Runningtarrens/Msweep/pics/PXL_20230211_223605693.jpg

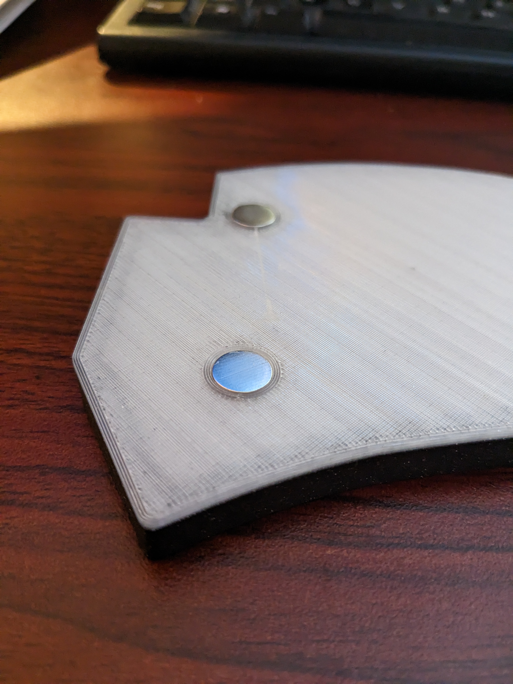
pics/PXL_20230211_223605693.jpg
