Runningtarrens/Msweep/pics/PXL_20230214_120325420.jpg

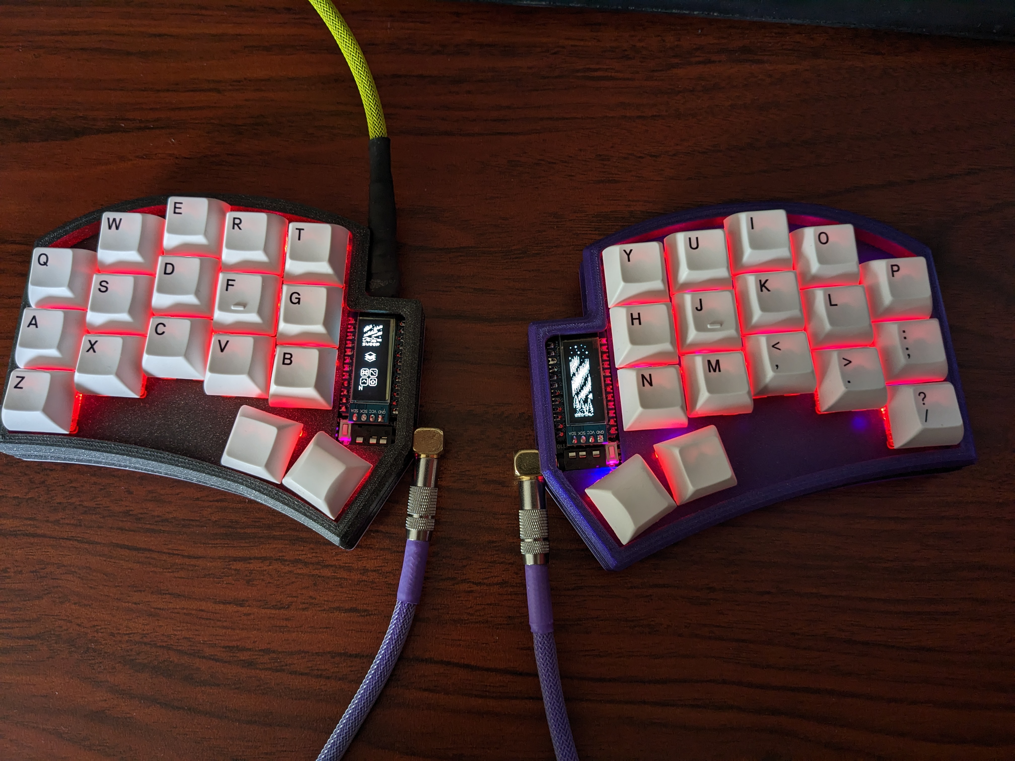
pics/PXL_20230214_120325420.jpg
