Runningtarrens/Msweep/pics/PXL_20230214_122314596.jpg

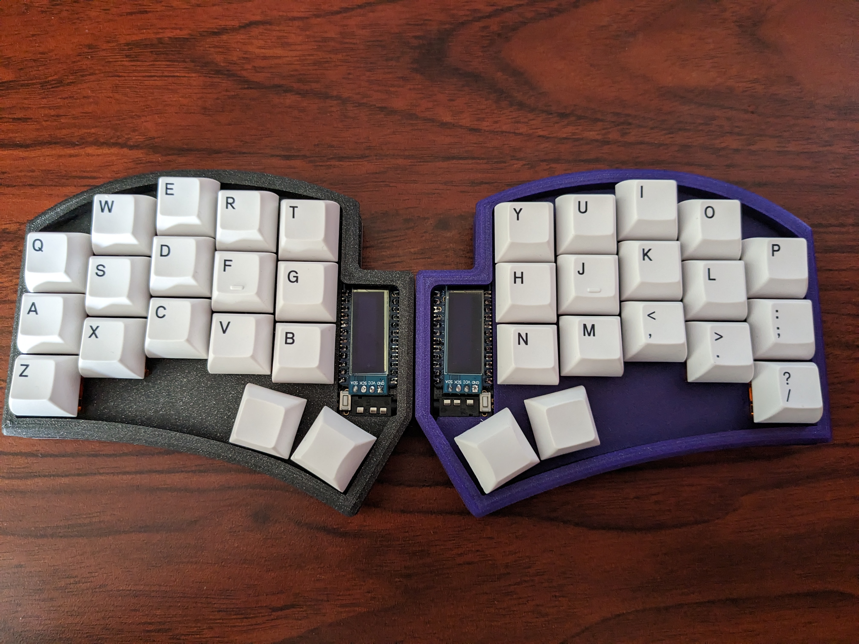
pics/PXL_20230214_122314596.jpg
