Runningtarrens/Msweep/pics/PXL_20230214_122454524.jpg

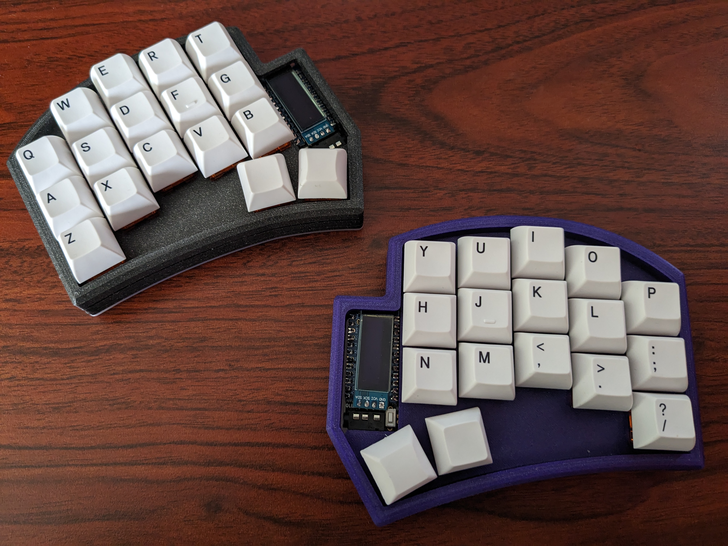
pics/PXL_20230214_122454524.jpg
