Runningtarrens/Msweep/pics/PXL_20230216_065255677.jpg

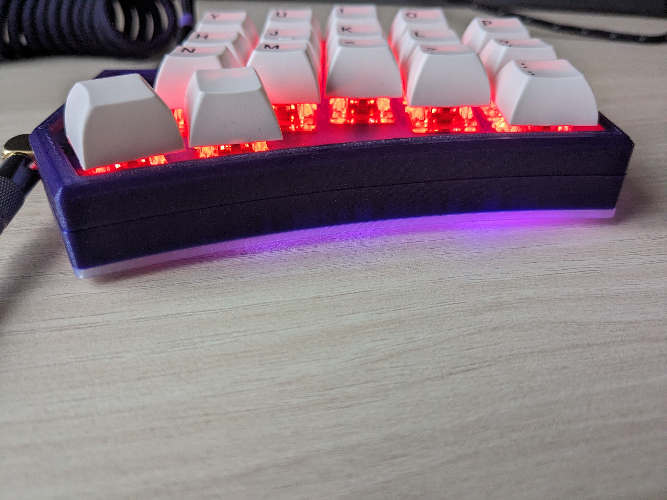
pics/PXL_20230216_065255677.jpg
