Runningtarrens/Msweep/pics/PXL_20230216_065311987.jpg

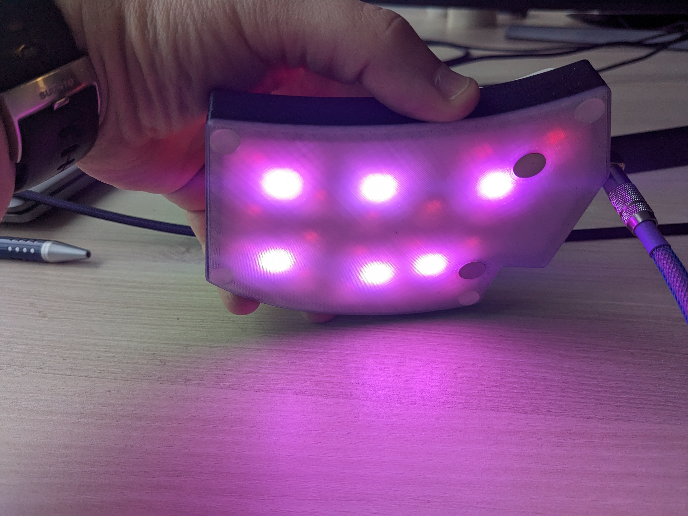
pics/PXL_20230216_065311987.jpg
