Runningtarrens/Msweep/pics/PXL_20230216_065402913.jpg

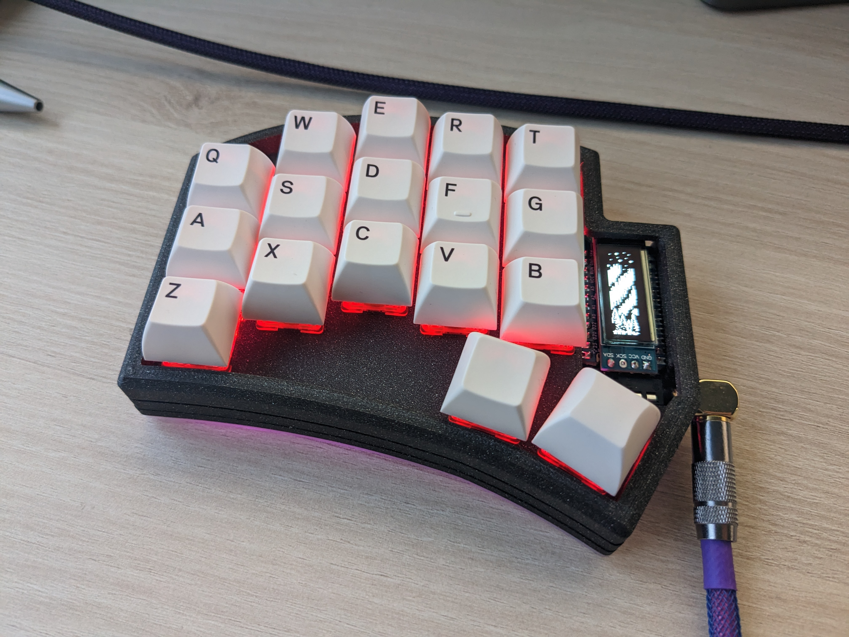
pics/PXL_20230216_065402913.jpg
