Runningtarrens/Msweep/pics/PXL_20230216_065406352.jpg

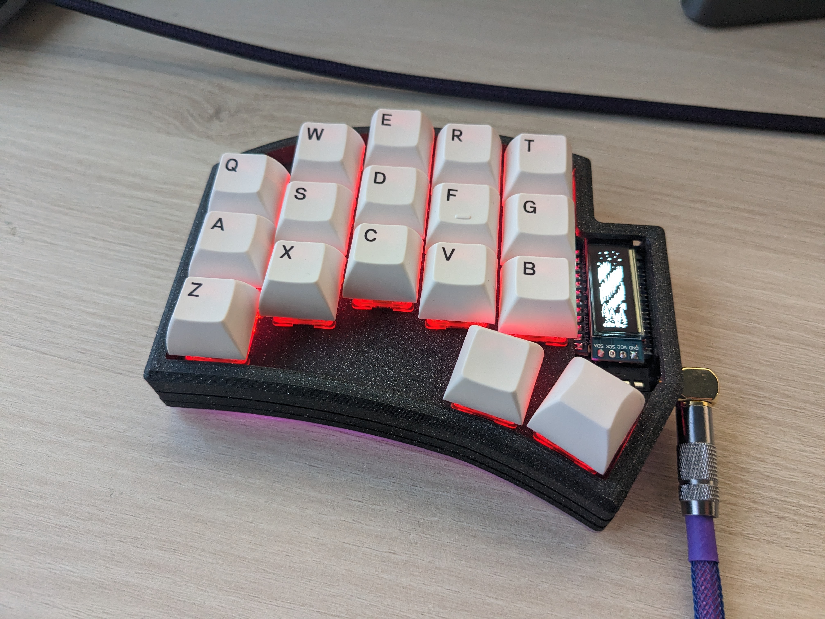
pics/PXL_20230216_065406352.jpg
