Runningtarrens/Msweep/pics/PXL_20230216_125020288.jpg

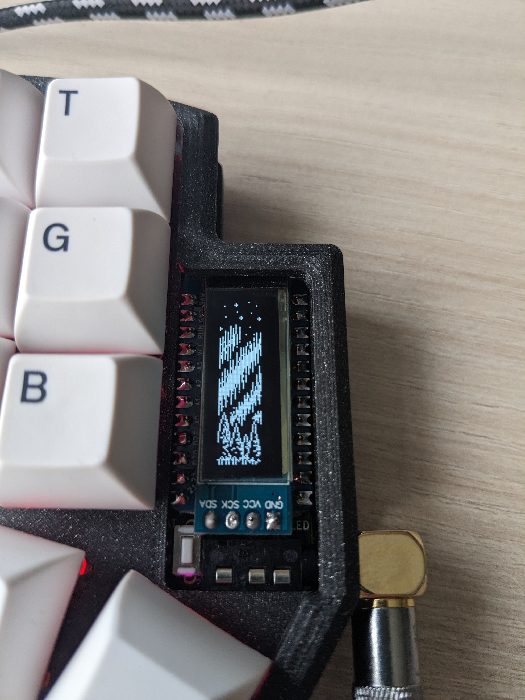
pics/PXL_20230216_125020288.jpg
