Runningtarrens/Msweep/pics/PXL_20230217_055919639.jpg

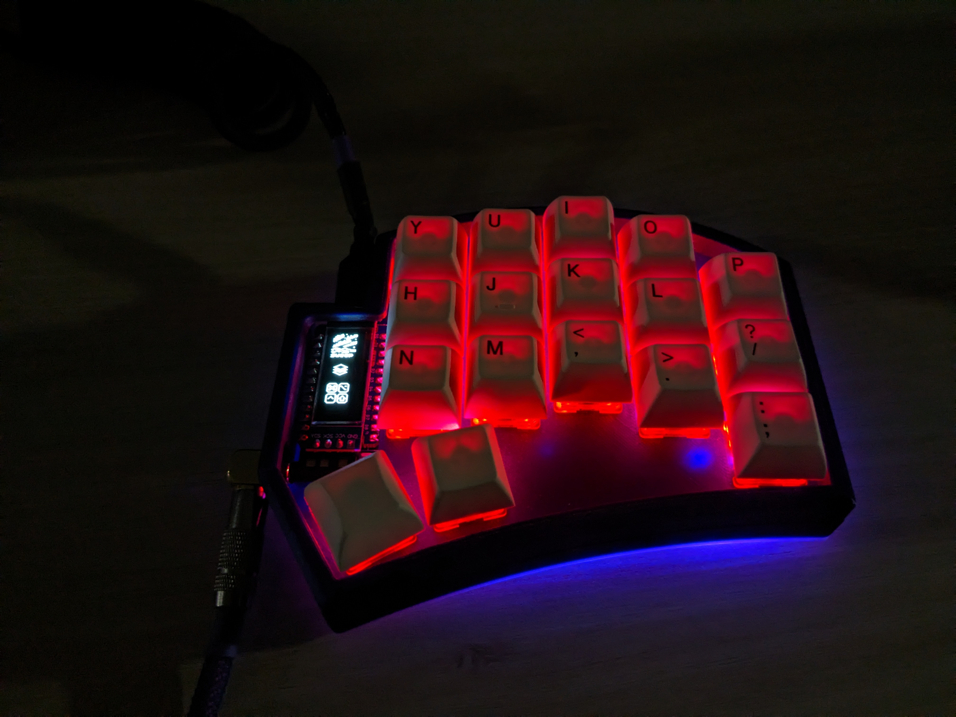
pics/PXL_20230217_055919639.jpg
