Runningtarrens/Msweep/pics/PXL_20230217_123806522.jpg

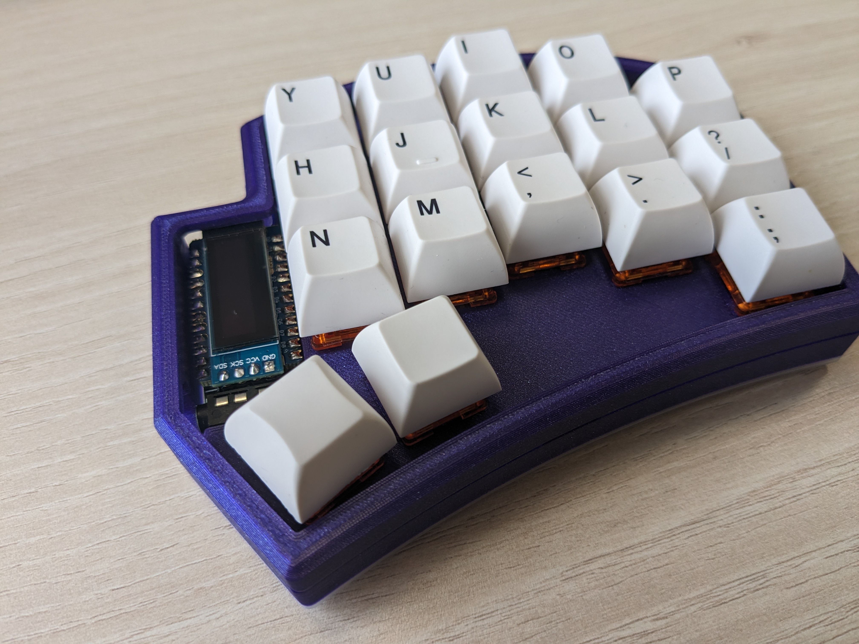
pics/PXL_20230217_123806522.jpg
