Runningtarrens/Msweep/pics/PXL_20230217_124105547.jpg

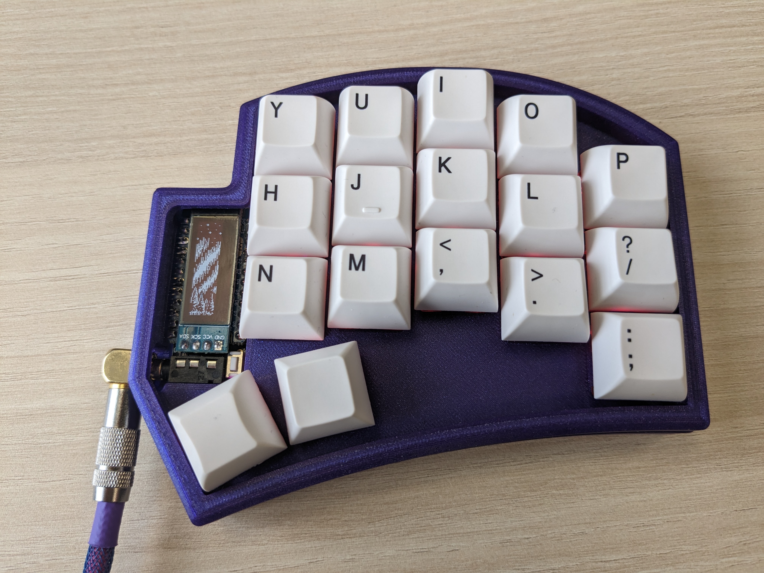
pics/PXL_20230217_124105547.jpg
