Runningtarrens/Msweep/pics/PXL_20230217_124110860.jpg

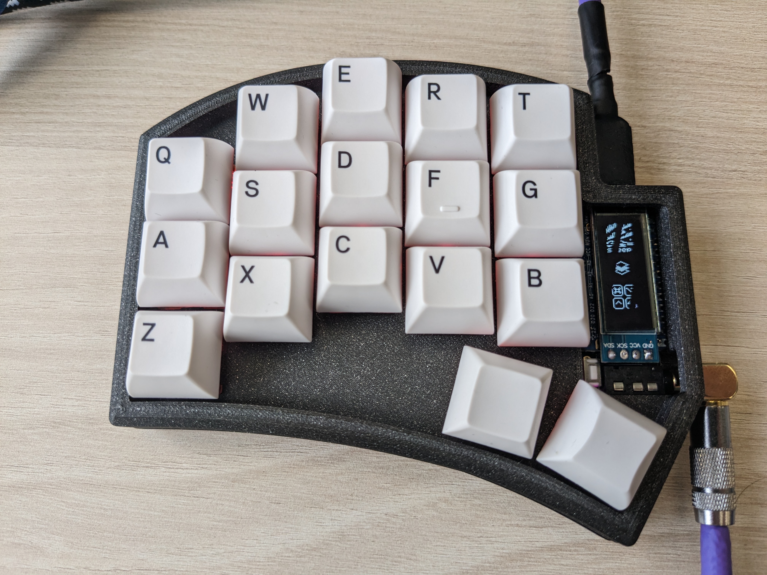
pics/PXL_20230217_124110860.jpg
