Runningtarrens/Msweep/pics/PXL_20230221_140735402.jpg

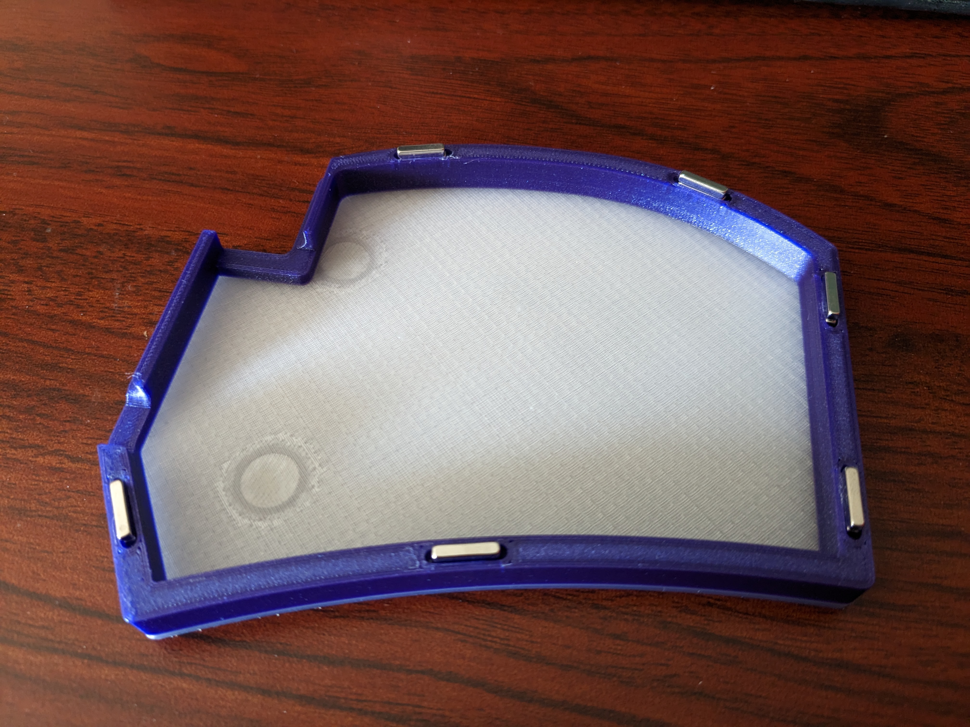
pics/PXL_20230221_140735402.jpg
