Runningtarrens/Msweep/pics/PXL_20230221_140748660.jpg

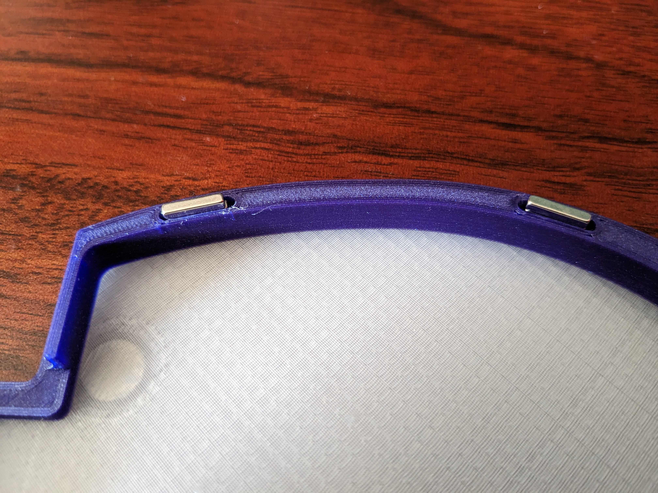
pics/PXL_20230221_140748660.jpg
