Runningtarrens/Msweep/pics/PXL_20230221_140926670.jpg

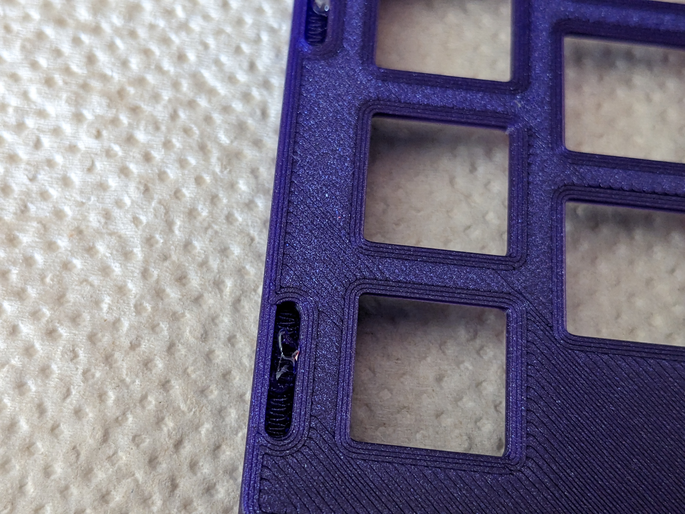
pics/PXL_20230221_140926670.jpg
