Runningtarrens/Msweep/pics/PXL_20230221_140929598.jpg

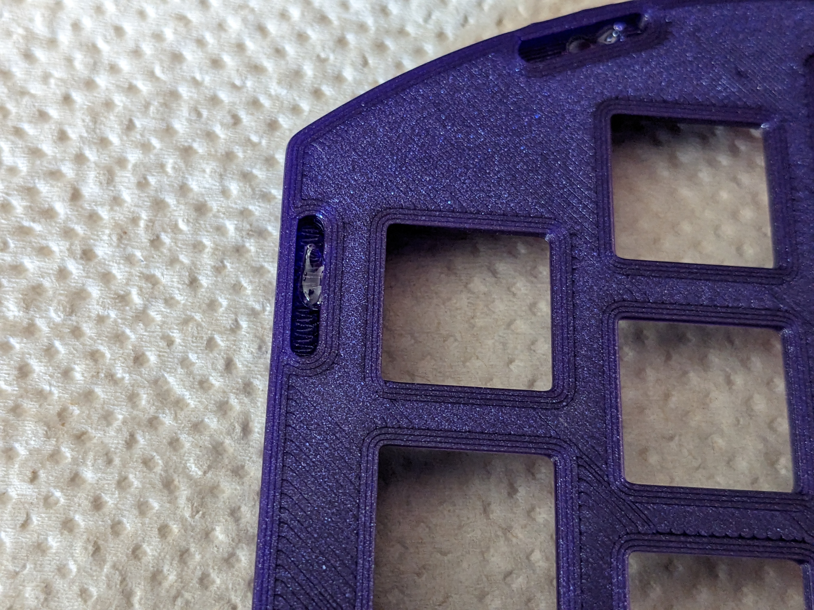
pics/PXL_20230221_140929598.jpg
