Runningtarrens/Msweep/pics/PXL_20230221_141020471.jpg

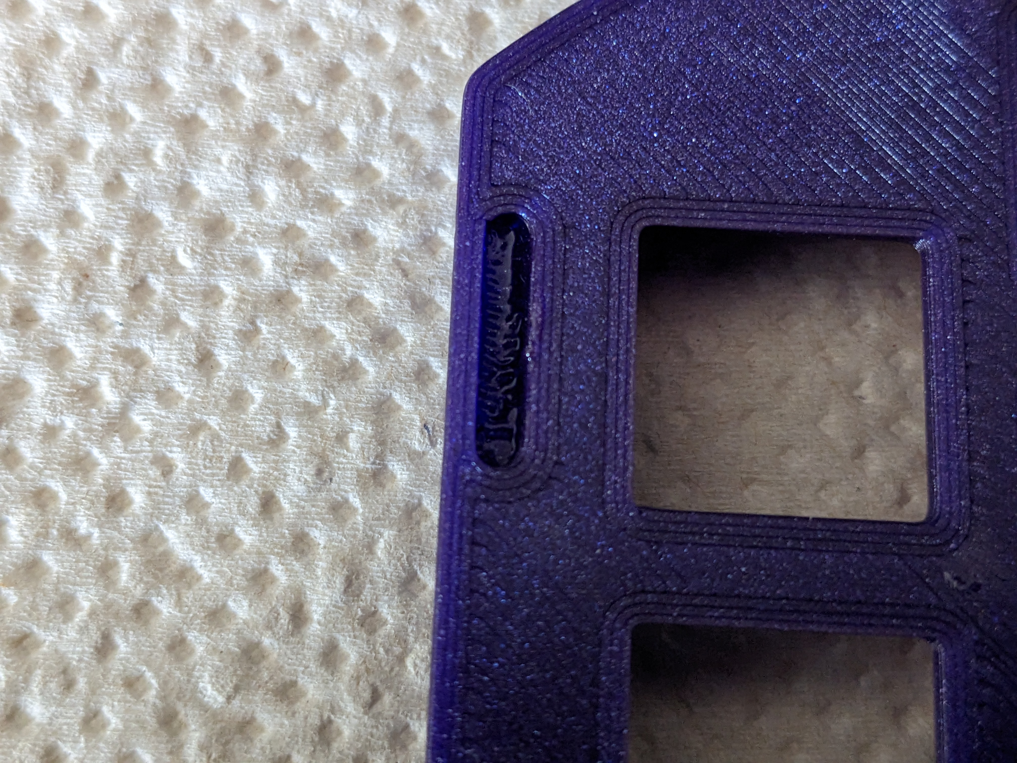
pics/PXL_20230221_141020471.jpg
