Runningtarrens/Msweep/pics/PXL_20230222_172946176.jpg

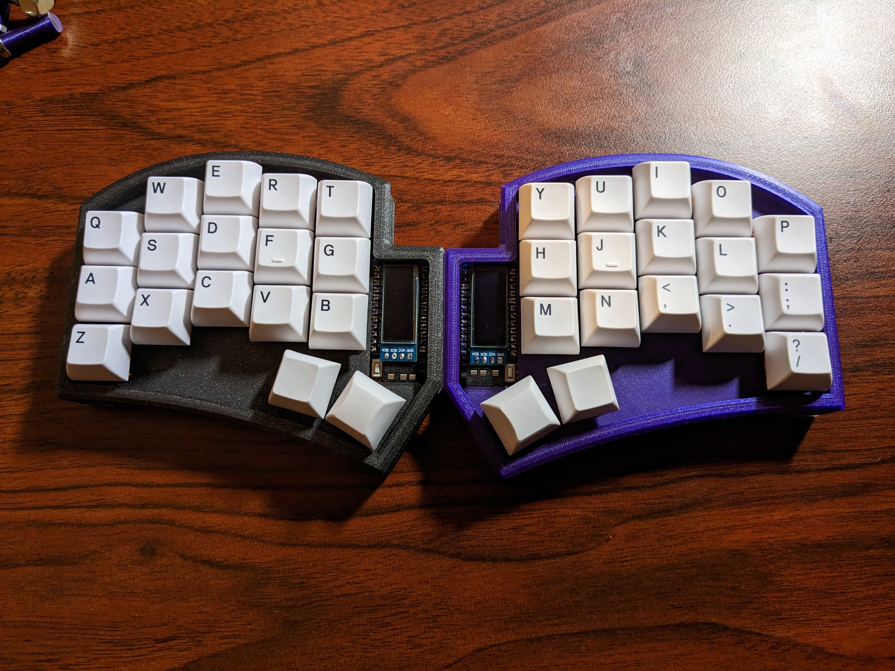
pics/PXL_20230222_172946176.jpg
