Runningtarrens/Msweep/pics/PXL_20230222_173118270.jpg

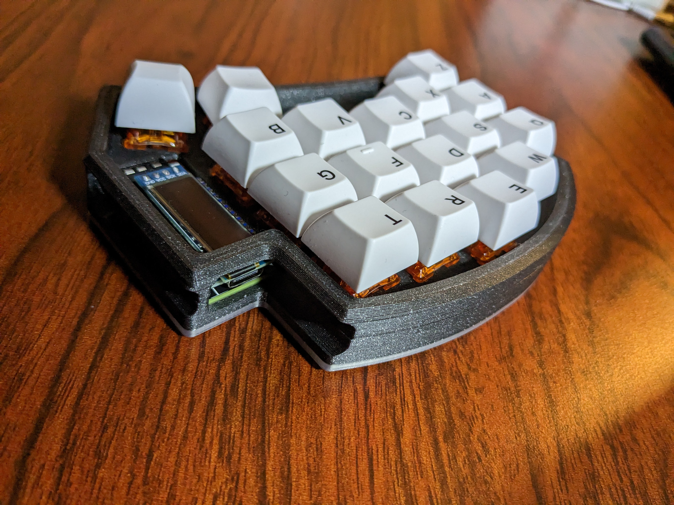
pics/PXL_20230222_173118270.jpg
