Runningtarrens/Msweep/pics/PXL_20230222_173219100.jpg

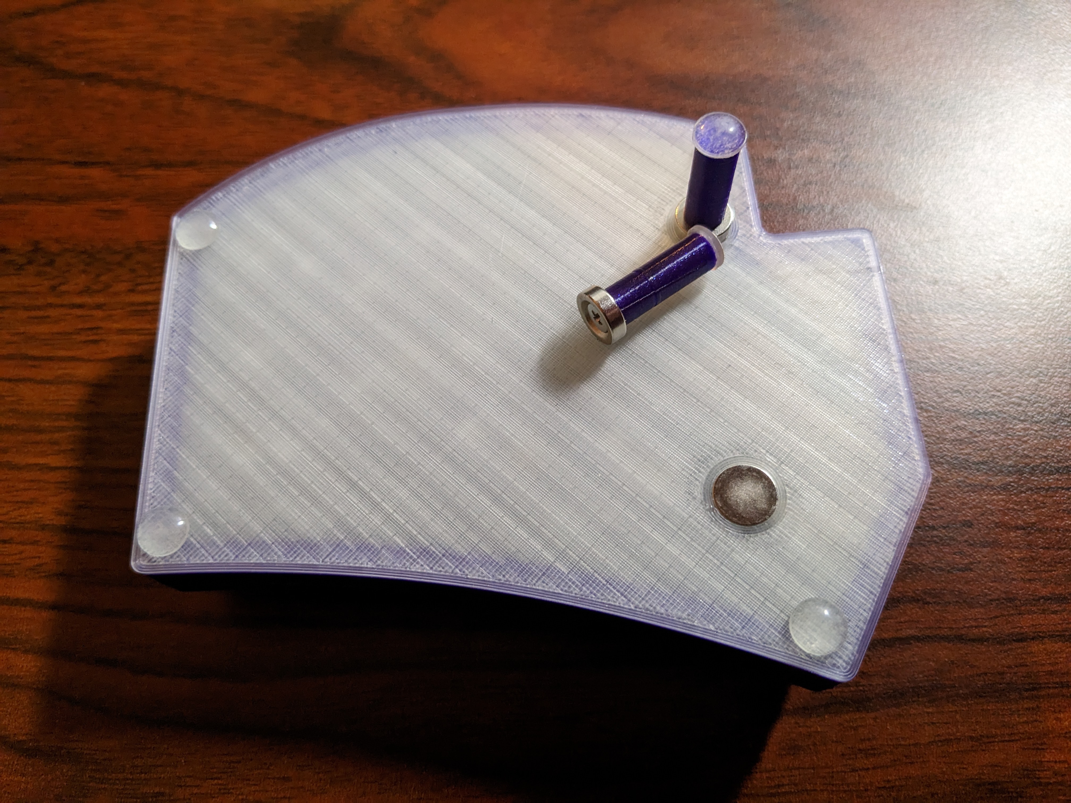
pics/PXL_20230222_173219100.jpg
